Siliconinsid/SCSIknifePocket/schematics/SCSIknife_pocket.kicad_sch

## KiCad design schematics/SCSIknife_pocket.kicad_sch (2025-01-19)

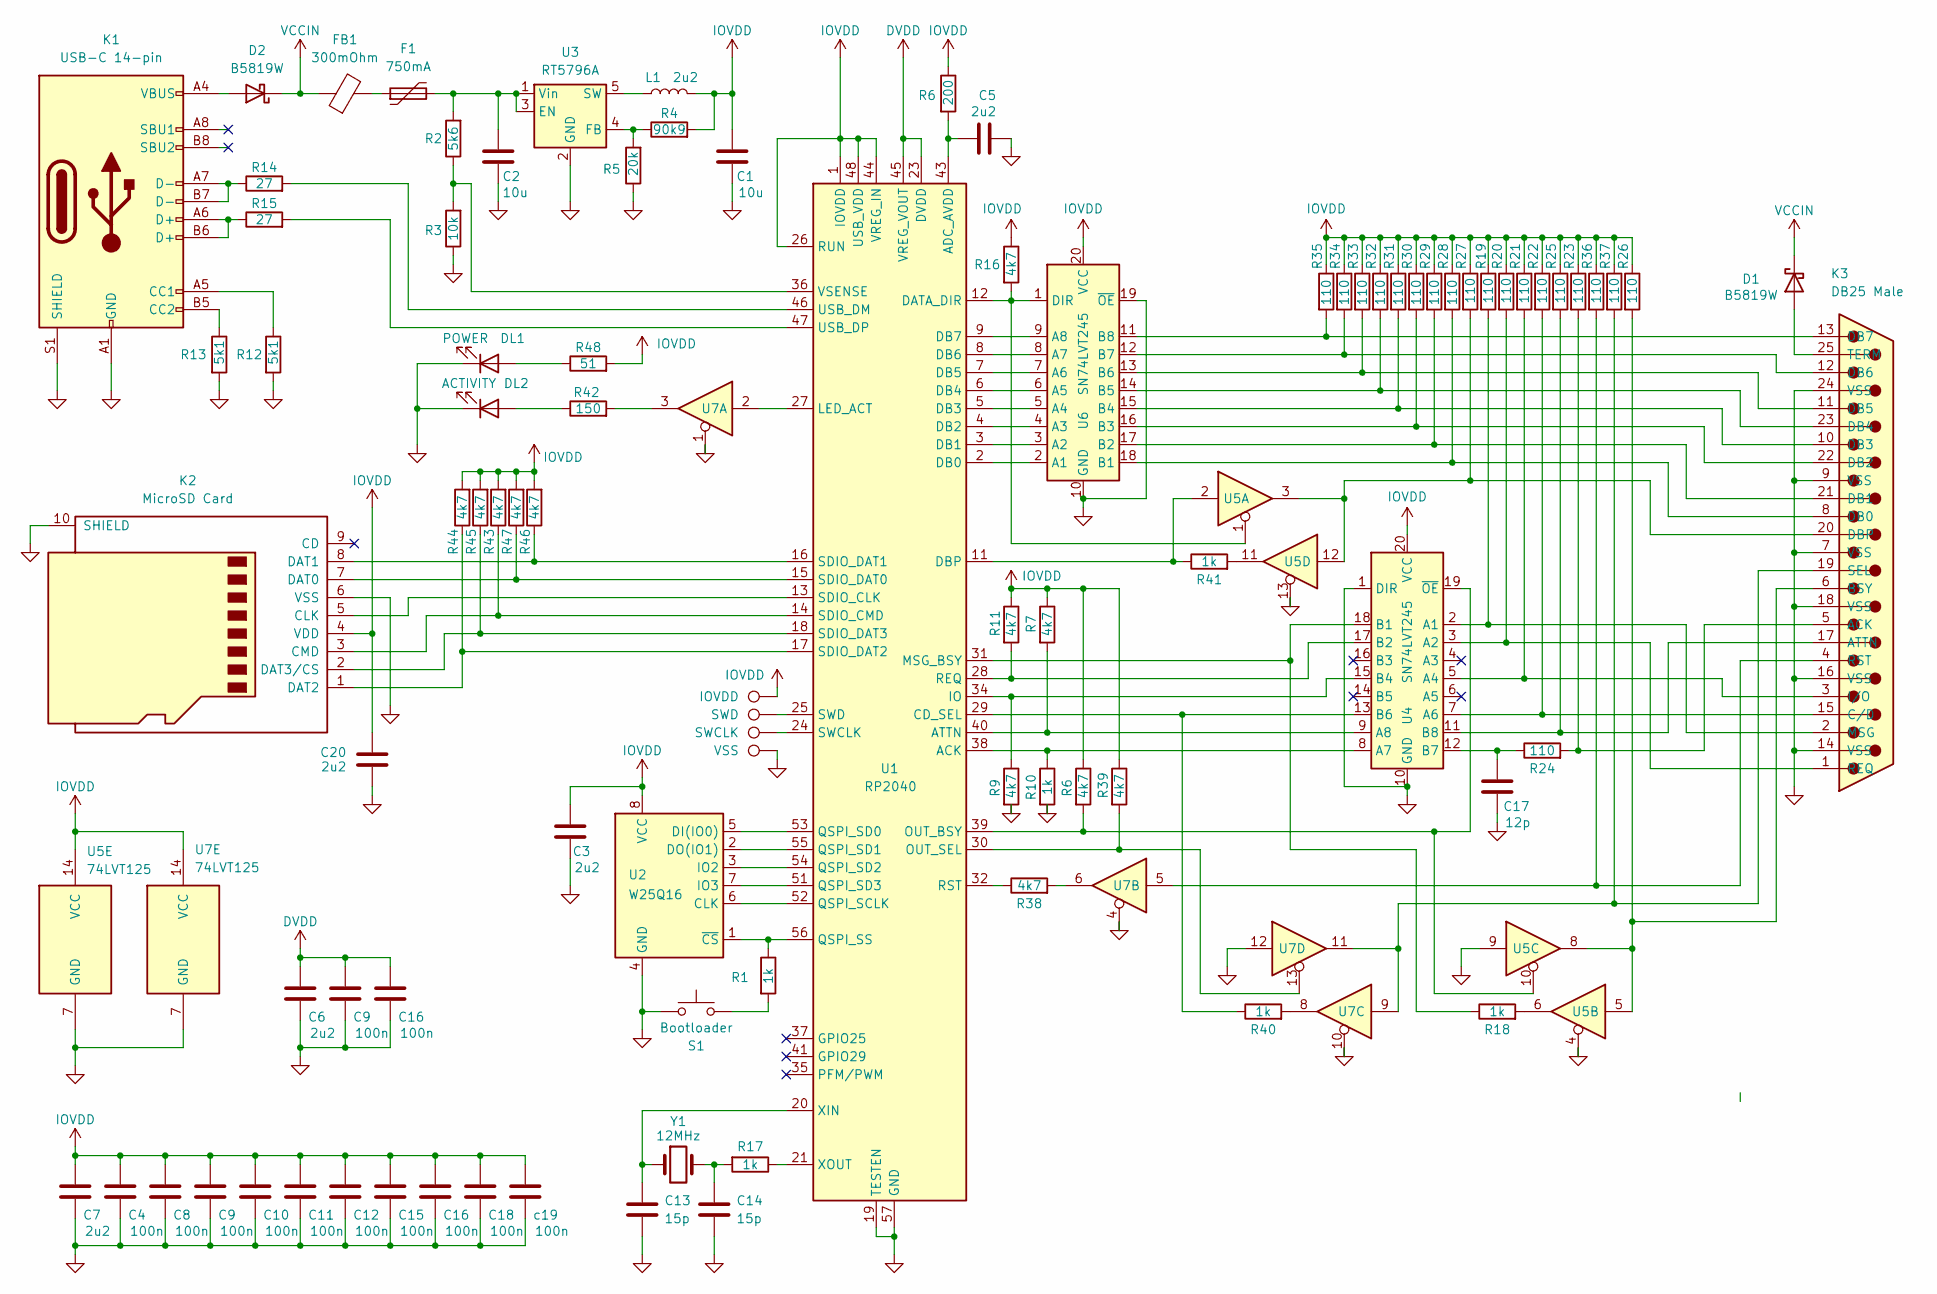
[picture p14: schematic SCSIknife_pocket.kicad_sch]

Parts:
C1, C2: 10u
C3, C5, C6, C7, C20: 2u2
C4, C8, C9, C10, C11, C12, C15, C16, C18: 100n
C13, C14: 15p
C17: 12p
D1, D2: B5819W; D_DO-41_SOD81_P10.16mm_Horizontal
DL1: POWER
DL2: ACTIVITY
F1: 750mA
FB1: 300mOhm
K1: USB-C 14-pin
K2: MicroSD Card
K3: DB25 Male
L1: 2u2
R1, R10, R17, R18, R40, R41: 1k
R2: 5k6
R3: 10k
R4: 90k9
R5: 20k
R6, R7, R9, R11, R16, R38, R39, R43, R44, R45, R46, R47: 4k7
R12, R13: 5k1
R14, R15: 27
R19, R20, R21, R22, R23, R24, R25, R26, R27, R28, R29, R30, R31, R32, R33, R34, R35, R36, R37: 110
R42: 150
R48: 51
S1: Bootloader
TP1: IOVDD
TP2: SWD
TP3: SWCLK
TP4: VSS
U1: RP2040; QFN-56-1EP_7x7mm_P0.4mm_EP3.2x3.2mm
U2: W25Q16; SOIC-8_5.23x5.23mm_P1.27mm
U3: RT5796A; TSOT-23-5
U4, U6: SN74LVT245; TSSOP-20_4.4x6.5mm_P0.65mm
U5, U7: 74LVT125
Y1: 12MHz
c19: 100n

Connections:
DVDD: C6.1, C9.1, C16.1, U1.23 (DVDD), U1.45 (VREG_VOUT), U1.50 (DVDD)
GND: C1.2, C2.2, C3.2, C4.2, C5.2, C6.2, C7.2, C8.2, C9.2, C10.2, C11.2, C12.2, C13.2, C14.2, C15.2, C16.2, C17.2, C18.2, C20.1, DL1.1 (K), DL2.1 (K), K1.A1 (GND), K1.A12 (GND), K1.B1 (GND), K1.B12 (GND), K1.S1 (SHIELD), K2.6 (VSS), K2.10 (SHIELD), K3.7 (VSS), K3.9 (VSS), K3.14 (VSS), K3.16 (VSS), K3.18 (VSS), K3.24 (VSS), R3.1, R5.1, R9.2, R10.2, R12.2, R13.2, S1.1, TP4.1, U1.19 (TESTEN), U1.57 (GND), U2.4 (GND), U3.2 (GND), U4.1 (DIR), U4.10 (GND), U5.4, U5.7 (GND), U5.9, U5.13, U6.10 (GND), U6.19 (~OE), U7.1, U7.4, U7.7 (GND), U7.10, U7.12, c19.2
IOVDD: C1.1, C3.1, C4.1, C7.1, C8.1, C9.1, C10.1, C11.1, C12.1, C15.1, C16.1, C18.1, C20.2, K2.4 (VDD), L1.2, R4.2, R6.1, R7.1, R11.1, R16.1, R19.1, R20.1, R21.1, R22.1, R23.1, R25.1, R26.1, R27.1, R28.1, R29.1, R30.1, R31.1, R32.1, R33.1, R34.1, R35.1, R36.1, R37.1, R39.1, R43.2, R44.2, R45.2, R46.2, R47.2, R48.2, TP1.1, U1.1 (IOVDD), U1.10 (IOVDD), U1.22 (IOVDD), U1.26 (RUN), U1.33 (IOVDD), U1.42 (IOVDD), U1.44 (VREG_IN), U1.48 (USB_VDD), U1.49 (IOVDD), U2.8 (VCC), U4.20 (VCC), U5.14 (VCC), U6.20 (VCC), U7.14 (VCC), c19.1
unnamed: C2.1, F1.2, R2.2, U3.1 (Vin), U3.3 (EN)
unnamed: C5.1, R6.2, U1.43 (ADC_AVDD)
unnamed: C13.1, U1.20 (XIN), Y1.1
unnamed: C14.1, R17.2, Y1.2
unnamed: C17.1, R24.1, U4.12 (B7)
unnamed: D1.2 (A), K3.25 (TERM)
unnamed: D2.2 (A), K1.A4 (VBUS), K1.A9 (VBUS), K1.B4 (VBUS), K1.B9 (VBUS)
unnamed: DL1.2 (A), R48.1
unnamed: DL2.2 (A), R42.1
unnamed: F1.1, FB1.2
unnamed: K1.A5 (CC1), R12.1
unnamed: K1.A6 (D+), K1.B6 (D+), R15.1
unnamed: K1.A7 (D-), K1.B7 (D-), R14.1
unnamed: K1.B5 (CC2), R13.1
unnamed: K2.1 (DAT2), R44.1, U1.17 (SDIO_DAT2)
unnamed: K2.2 (DAT3/CS), R45.1, U1.18 (SDIO_DAT3)
unnamed: K2.3 (CMD), R43.1, U1.14 (SDIO_CMD)
unnamed: K2.5 (CLK), U1.13 (SDIO_CLK)
unnamed: K2.7 (DAT0), R47.1, U1.15 (SDIO_DAT0)
unnamed: K2.8 (DAT1), R46.1, U1.16 (SDIO_DAT1)
unnamed: K3.1 (REQ), R20.2, U4.3 (A2)
unnamed: K3.2 (MSG), R19.2, U4.2 (A1)
unnamed: K3.3 (I/O), R21.2, U4.5 (A4)
unnamed: K3.4 (RST), R36.2, U7.5
unnamed: K3.5 (ACK), R23.2, R24.2
unnamed: K3.6 (BSY), R26.2, U5.5, U5.8
unnamed: K3.8 (DB0), R28.2, U6.18 (B1)
unnamed: K3.10 (DB3), R31.2, U6.15 (B4)
unnamed: K3.11 (DB5), R33.2, U6.13 (B6)
unnamed: K3.12 (DB6), R34.2, U6.12 (B7)
unnamed: K3.13 (DB7), R35.2, U6.11 (B8)
unnamed: K3.15 (C/D), R22.2, U4.7 (A6)
unnamed: K3.17 (ATTN), R25.2, U4.11 (B8)
unnamed: K3.19 (SEL), R37.2, U7.9, U7.11
unnamed: K3.20 (DBP), R27.2, U5.3, U5.12
unnamed: K3.21 (DB1), R29.2, U6.17 (B2)
unnamed: K3.22 (DB2), R30.2, U6.16 (B3)
unnamed: K3.23 (DB4), R32.2, U6.14 (B5)
unnamed: L1.1, U3.5 (SW)
unnamed: R1.1, U1.56 (QSPI_SS), U2.1 (~CS)
unnamed: R1.2, S1.2
unnamed: R2.1, R3.2, U1.36 (VSENSE)
unnamed: R4.1, R5.2, U3.4 (FB)
unnamed: R6.2, U1.39 (OUT_BSY), U4.19 (~OE), U5.10
unnamed: R7.2, U1.40 (ATTN), U4.9 (A8)
unnamed: R9.1, U1.34 (IO), U4.15 (B4)
unnamed: R10.1, U1.38 (ACK), U4.8 (A7)
unnamed: R11.2, U1.28 (REQ), U4.17 (B2)
unnamed: R14.2, U1.46 (USB_DM)
unnamed: R15.2, U1.47 (USB_DP)
unnamed: R16.2, U1.12 (DATA_DIR), U5.1, U6.1 (DIR)
unnamed: R17.1, U1.21 (XOUT)
unnamed: R18.1, U1.31 (MSG_BSY), U4.18 (B1)
unnamed: R18.2, U5.6
unnamed: R38.1, U1.32 (RST)
unnamed: R38.2, U7.6
unnamed: R39.2, U1.30 (OUT_SEL), U7.13
unnamed: R40.1, U1.29 (CD_SEL), U4.13 (B6)
unnamed: R40.2, U7.8
unnamed: R41.1, U1.11 (DBP), U5.2
unnamed: R41.2, U5.11
unnamed: R42.2, U7.3
unnamed: TP2.1, U1.25 (SWD)
unnamed: TP3.1, U1.24 (SWCLK)
unnamed: U1.2 (DB0), U6.2 (A1)
unnamed: U1.3 (DB1), U6.3 (A2)
unnamed: U1.4 (DB2), U6.4 (A3)
unnamed: U1.5 (DB3), U6.5 (A4)
unnamed: U1.6 (DB4), U6.6 (A5)
unnamed: U1.7 (DB5), U6.7 (A6)
unnamed: U1.8 (DB6), U6.8 (A7)
unnamed: U1.9 (DB7), U6.9 (A8)
unnamed: U1.27 (LED_ACT), U7.2
unnamed: U1.51 (QSPI_SD3), U2.7 (IO3)
unnamed: U1.52 (QSPI_SCLK), U2.6 (CLK)
unnamed: U1.53 (QSPI_SD0), U2.5 (DI(IO0))
unnamed: U1.54 (QSPI_SD2), U2.3 (IO2)
unnamed: U1.55 (QSPI_SD1), U2.2 (DO(IO1))
VCCIN: D1.1 (K), D2.1 (K), FB1.1
